FOSSEE/KiCad-eSim/share/kicad/demos/custom_pads_test/custom_pads_test.kicad_pcb

## KiCad design share/kicad/demos/custom_pads_test/custom_pads_test.kicad_pcb (2025-06-14)

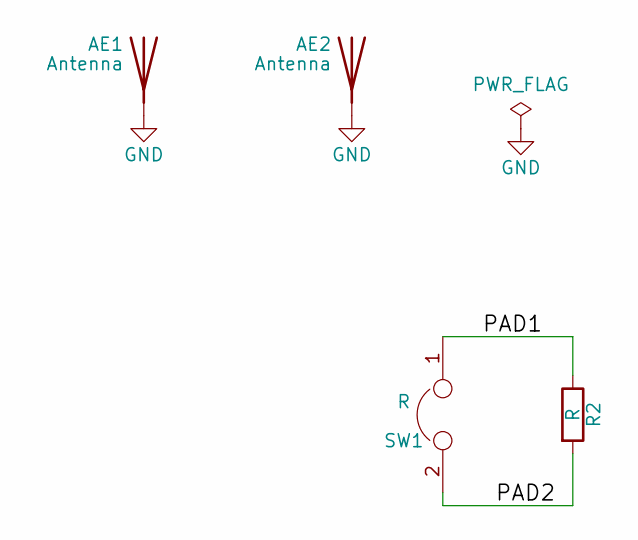
[picture p42: schematic custom_pads_test.kicad_sch]

Parts:
AE1, AE2: Antenna
R2: R
SW1: R

Connections:
/PAD1: R2.1, SW1.1
/PAD2: R2.2, SW1.2
GND: AE1.1 (A), AE2.1 (A)

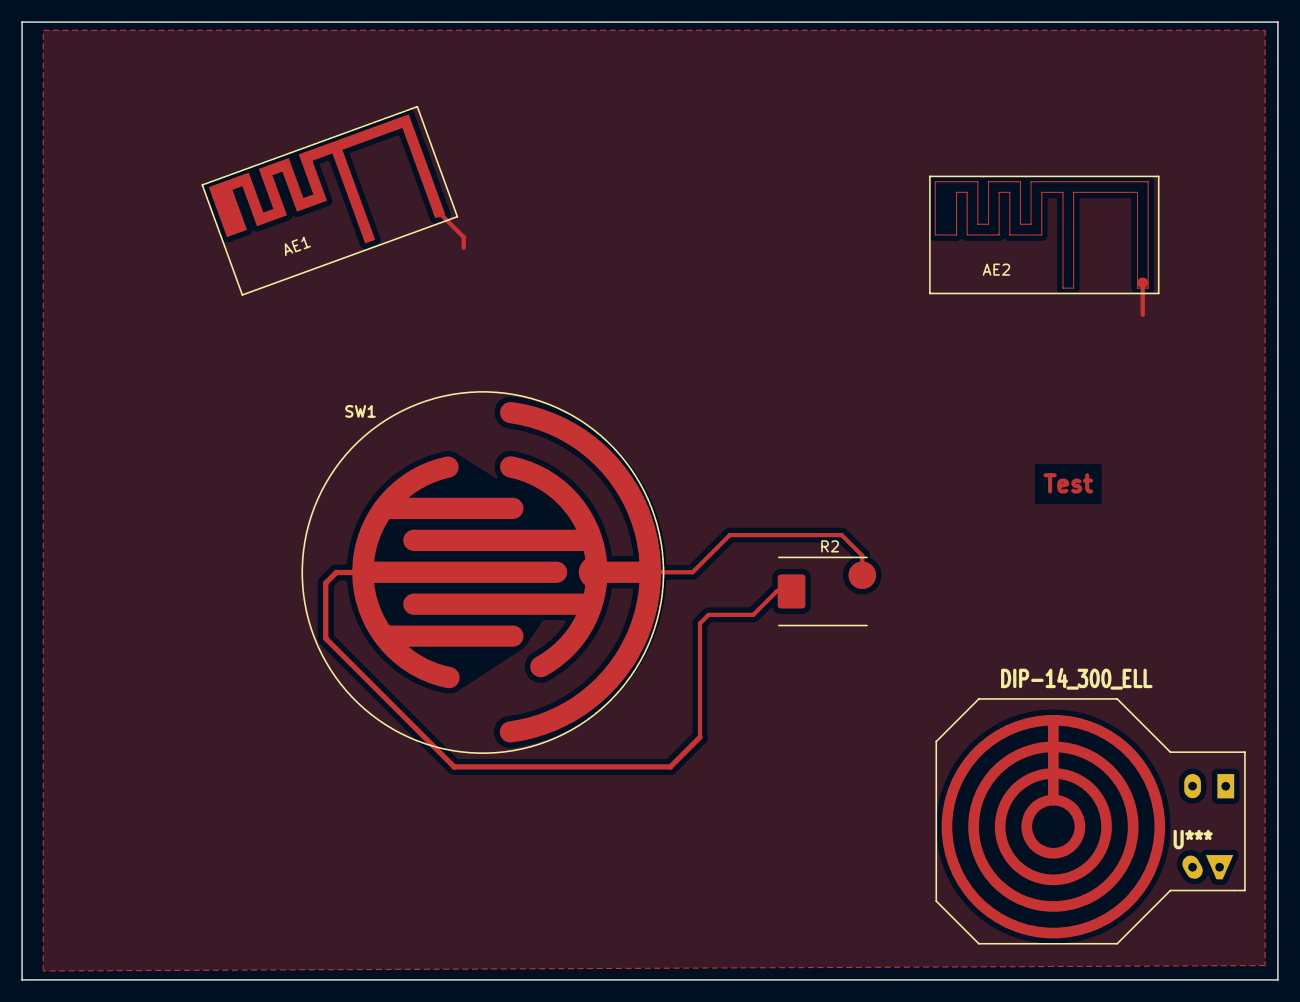
[picture p43: board custom_pads_test.kicad_pcb from above]

Board: 2 copper layers, 118.0 x 90.0 mm, 5 parts (0 on the bottom side), 3 nets.

Other parts of the board:
U***: DIP-14_300_ELL; DIP-14__300_ELL
