FOSSEE/KiCad-eSim/share/kicad/demos/simulation/laser_driver/laser_driver.kicad_sch

## KiCad design share/kicad/demos/simulation/laser_driver/laser_driver.kicad_sch (2025-06-14)

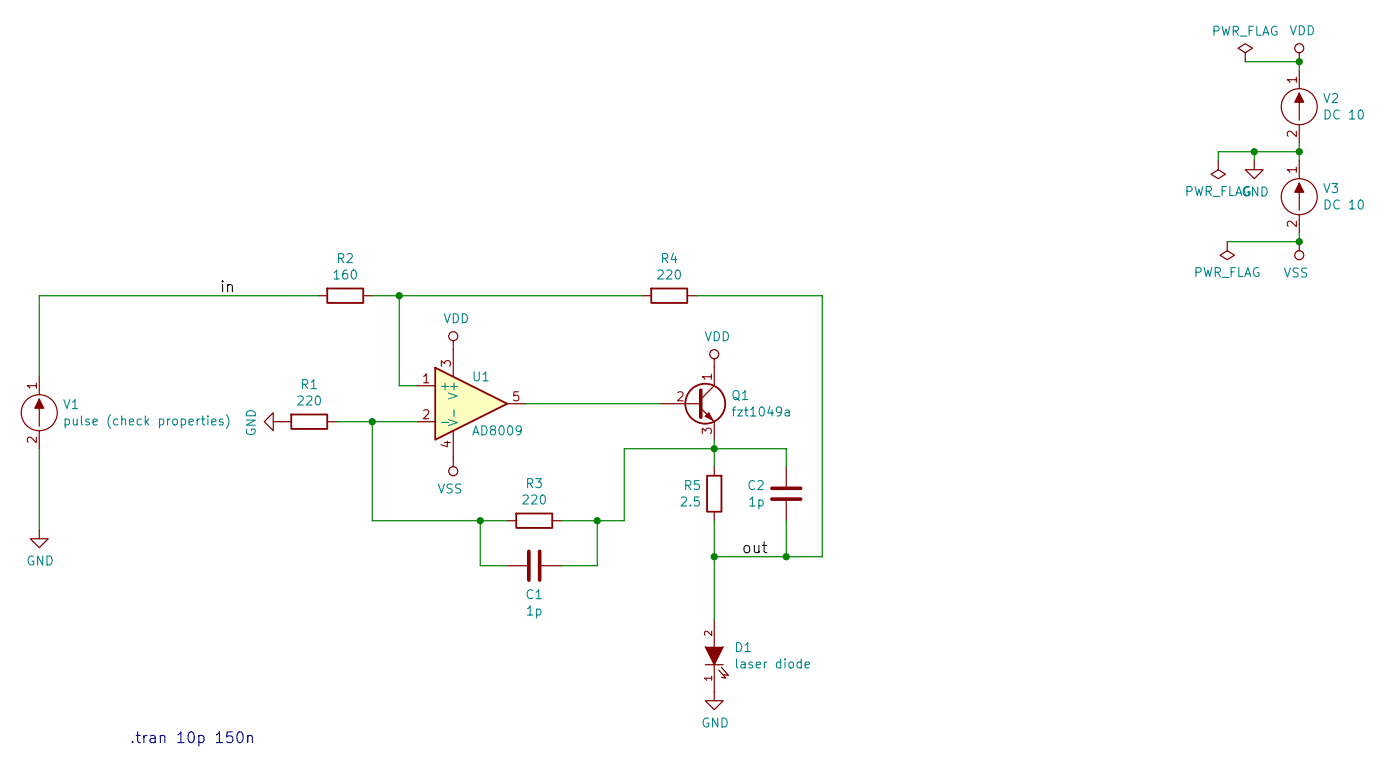
[picture p44: schematic laser_driver.kicad_sch]

Parts:
C1, C2: 1p
D1: laser diode
Q1: fzt1049a
R1, R3, R4: 220
R2: 160
R5: 2.5
U1: AD8009
V1: pulse (check properties)
V2, V3: DC 10

Connections:
GND: D1.1 (K), R1.2, V1.2, V2.2, V3.1
unnamed: C1.1, R1.1, R3.2, U1.2 (-)
unnamed: C1.2, C2.2, Q1.3 (E), R3.1, R5.2
unnamed: Q1.2 (B), U1.5
unnamed: R2.1, R4.2, U1.1 (+)
VDD: Q1.1 (C), U1.3 (V+), V2.1
VSS: U1.4 (V-), V3.2
in: R2.2, V1.1
out: C2.1, D1.2 (A), R4.1, R5.1

Notes on the sheet:
.tran 10p 150n
