FOSSEE/KiCad-eSim/share/kicad/demos/simulation/pspice/pspice.kicad_sch

## KiCad design share/kicad/demos/simulation/pspice/pspice.kicad_sch (2025-06-14)

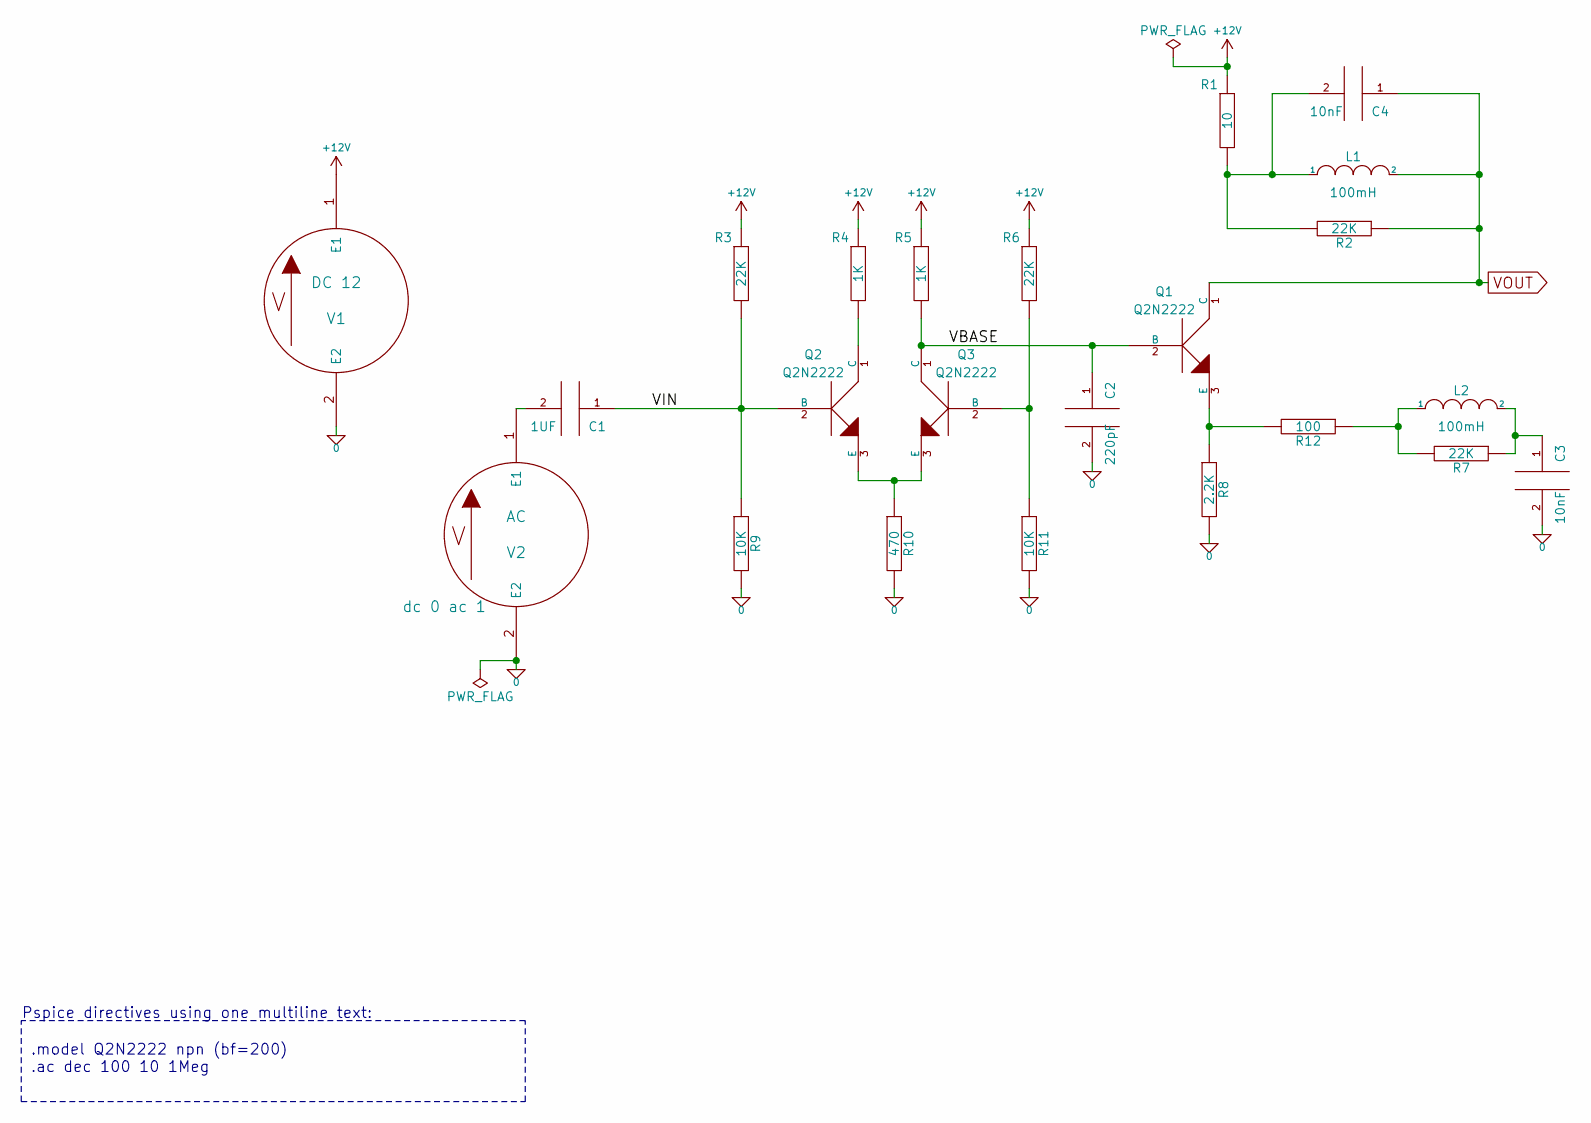
[picture p45: schematic pspice.kicad_sch]

Parts:
C1: 1UF
C2: 220pF
C3, C4: 10nF
L1, L2: 100mH
Q1, Q2, Q3: Q2N2222
R1: 10
R2, R3, R6, R7: 22K
R4, R5: 1K
R8: 2.2K
R9, R11: 10K
R10: 470
R12: 100
V1: DC 12
V2: AC

Connections:
0: C2.2, C3.2, R8.2, R9.2, R10.2, R11.2, V1.2 (E2), V2.2 (E2)
+12V: R1.1, R3.1, R4.1, R5.1, R6.1, V1.1 (E1)
unnamed: C1.2, V2.1 (E1)
unnamed: C3.1, L2.2, R7.1
unnamed: C4.2, L1.1, R1.2, R2.2
unnamed: L2.1, R7.2, R12.1
unnamed: Q1.3 (E), R8.1, R12.2
unnamed: Q2.1 (C), R4.2
unnamed: Q2.3 (E), Q3.3 (E), R10.1
unnamed: Q3.2 (B), R6.2, R11.1
VBASE: C2.1, Q1.2 (B), Q3.1 (C), R5.2
VIN: C1.1, Q2.2 (B), R3.2, R9.1
VOUT: C4.1, L1.2, Q1.1 (C), R2.1

Notes on the sheet:
Pspice directives using one multiline text:
.model Q2N2222 npn (bf=200) .ac dec 100 10 1Meg
