FOSSEE/KiCad-eSim/share/kicad/demos/simulation/rectifier/rectifier.kicad_sch

## KiCad design share/kicad/demos/simulation/rectifier/rectifier.kicad_sch (2025-06-14)

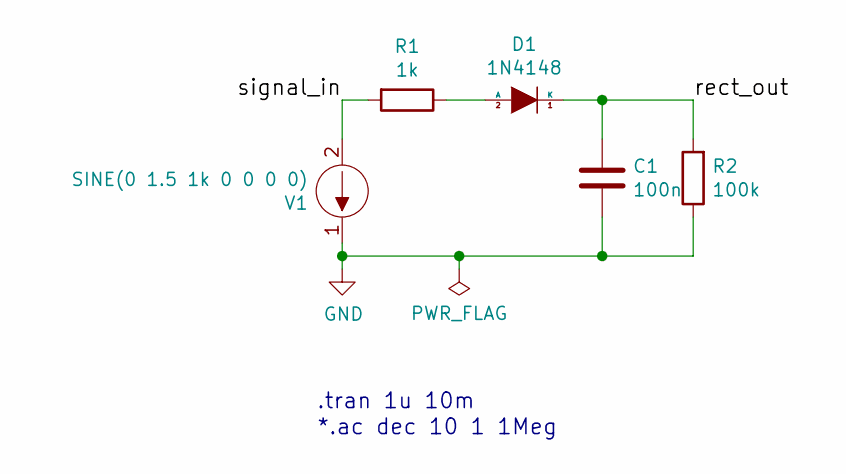
[picture p46: schematic rectifier.kicad_sch]

Parts:
C1: 100n
D1: 1N4148
R1: 1k
R2: 100k
V1: SINE(0 1.5 1k 0 0 0 0)

Connections:
GND: C1.2, R2.1, V1.1
unnamed: D1.2 (A), R1.1
rect_out: C1.1, D1.1 (K), R2.2
signal_in: R1.2, V1.2

Notes on the sheet:
.tran 1u 10m
*.ac dec 10 1 1Meg
