FOSSEE/KiCad-eSim/share/kicad/demos/simulation/sallen_key/sallen_key.kicad_sch

## KiCad design share/kicad/demos/simulation/sallen_key/sallen_key.kicad_sch (2025-06-14)

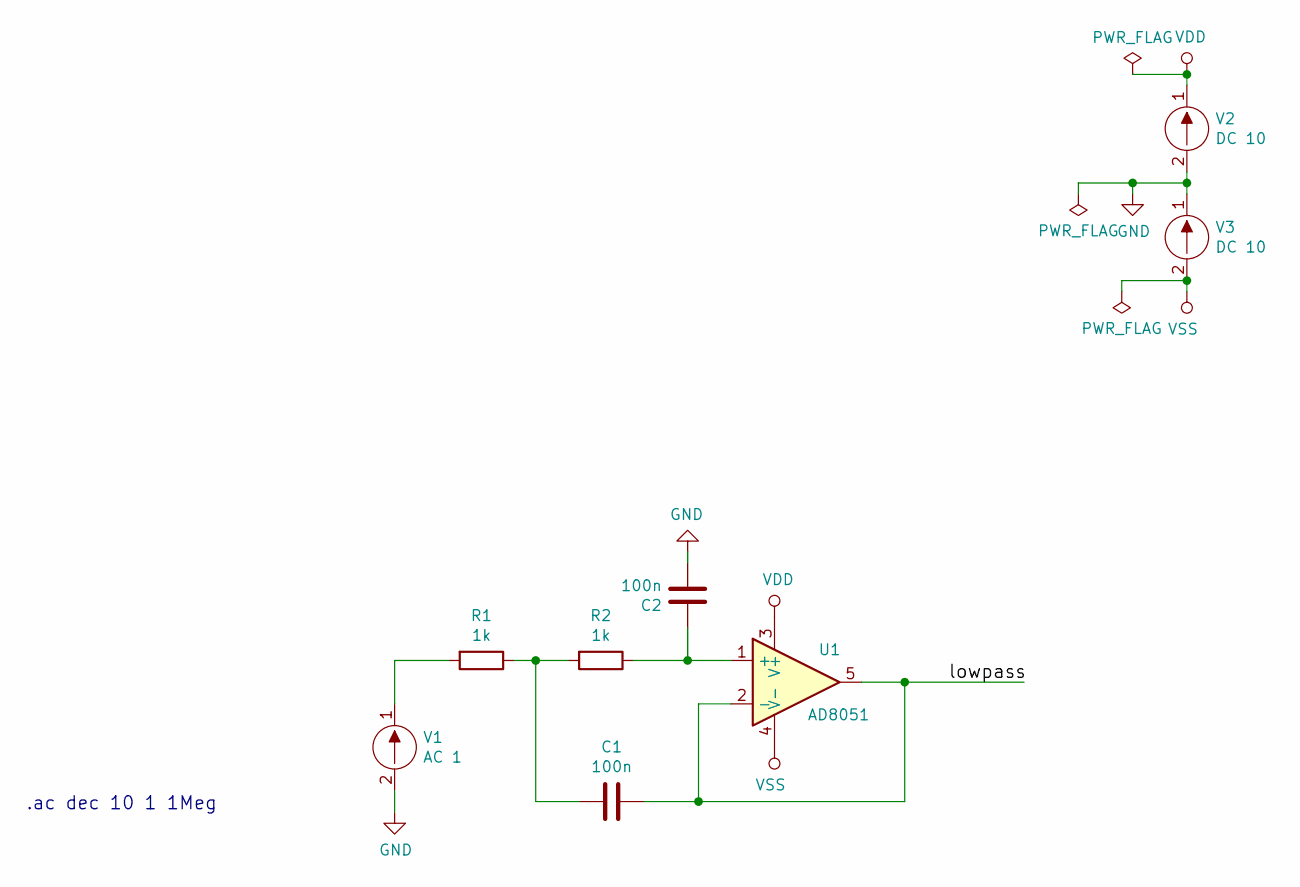
[picture p47: schematic sallen_key.kicad_sch]

Parts:
C1, C2: 100n
R1, R2: 1k
U1: AD8051
V1: AC 1
V2, V3: DC 10

Connections:
GND: C2.2, V1.2, V2.2, V3.1
unnamed: C1.2, R1.1, R2.2
unnamed: C2.1, R2.1, U1.1 (+)
unnamed: R1.2, V1.1
VDD: U1.3 (V+), V2.1
VSS: U1.4 (V-), V3.2
lowpass: C1.1, U1.2 (-), U1.5

Notes on the sheet:
.ac dec 10 1 1Meg
