FOSSEE/KiCad-eSim/share/kicad/demos/simulation/v_i_sources/v_i_sources.kicad_sch

## KiCad design share/kicad/demos/simulation/v_i_sources/v_i_sources.kicad_sch (2025-06-14)

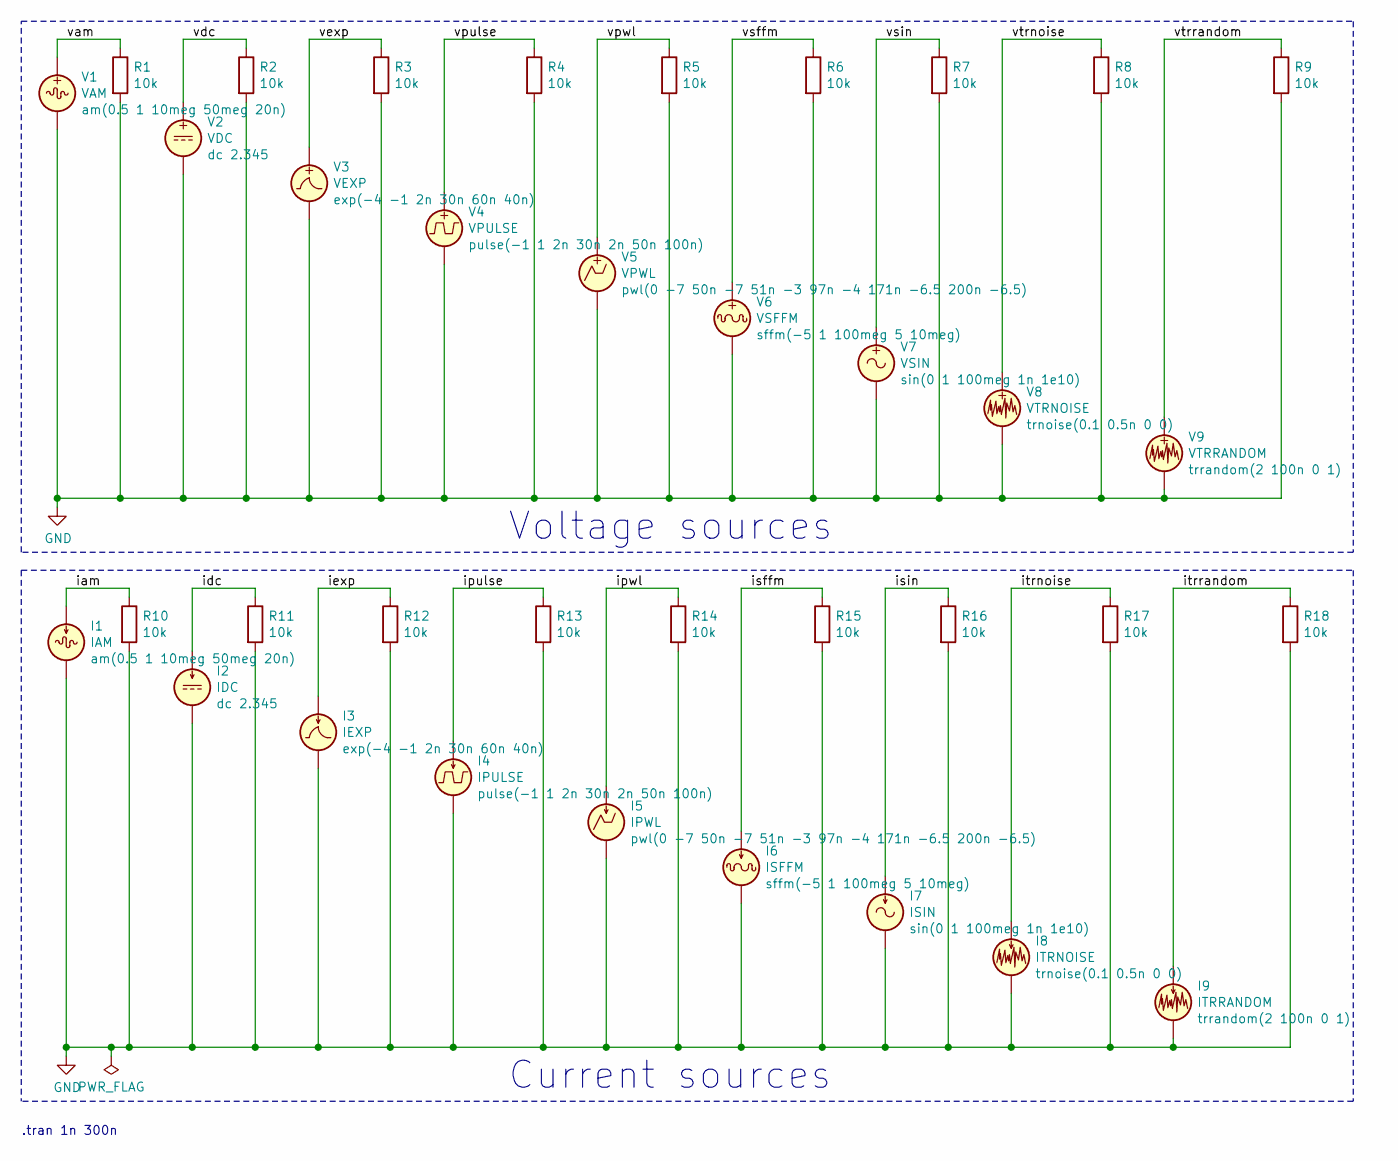
[picture p48: schematic v_i_sources.kicad_sch]

Parts:
I1: IAM
I2: IDC
I3: IEXP
I4: IPULSE
I5: IPWL
I6: ISFFM
I7: ISIN
I8: ITRNOISE
I9: ITRRANDOM
R1, R2, R3, R4, R5, R6, R7, R8, R9, R10, R11, R12, R13, R14, R15, R16, R17, R18: 10k
V1: VAM
V2: VDC
V3: VEXP
V4: VPULSE
V5: VPWL
V6: VSFFM
V7: VSIN
V8: VTRNOISE
V9: VTRRANDOM

Connections:
GND: I1.2, I2.2, I3.2, I4.2, I5.2, I6.2, I7.2, I8.2, I9.2, R1.2, R2.2, R3.2, R4.2, R5.2, R6.2, R7.2, R8.2, R9.2, R10.2, R11.2, R12.2, R13.2, R14.2, R15.2, R16.2, R17.2, R18.2, V1.2, V2.2, V3.2, V4.2, V5.2, V6.2, V7.2, V8.2, V9.2
iam: I1.1, R10.1
idc: I2.1, R11.1
iexp: I3.1, R12.1
ipulse: I4.1, R13.1
ipwl: I5.1, R14.1
isffm: I6.1, R15.1
isin: I7.1, R16.1
itrnoise: I8.1, R17.1
itrrandom: I9.1, R18.1
vam: R1.1, V1.1
vdc: R2.1, V2.1
vexp: R3.1, V3.1
vpulse: R4.1, V4.1
vpwl: R5.1, V5.1
vsffm: R6.1, V6.1
vsin: R7.1, V7.1
vtrnoise: R8.1, V8.1
vtrrandom: R9.1, V9.1

Notes on the sheet:
.tran 1n 300n
Voltage sources
Current sources
